DemonSlayer35/Stationnement_intelligent/data_parking/1images/5238d4bbb3d55c86db6f1e46-1600421843-1200x675.jpg

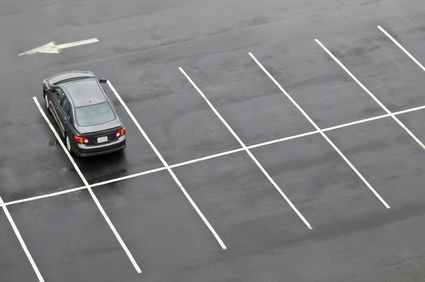
data_parking/1images/5238d4bbb3d55c86db6f1e46-1600421843-1200x675.jpg
