DemonSlayer35/Stationnement_intelligent/data_parking/1images/33248432.webp

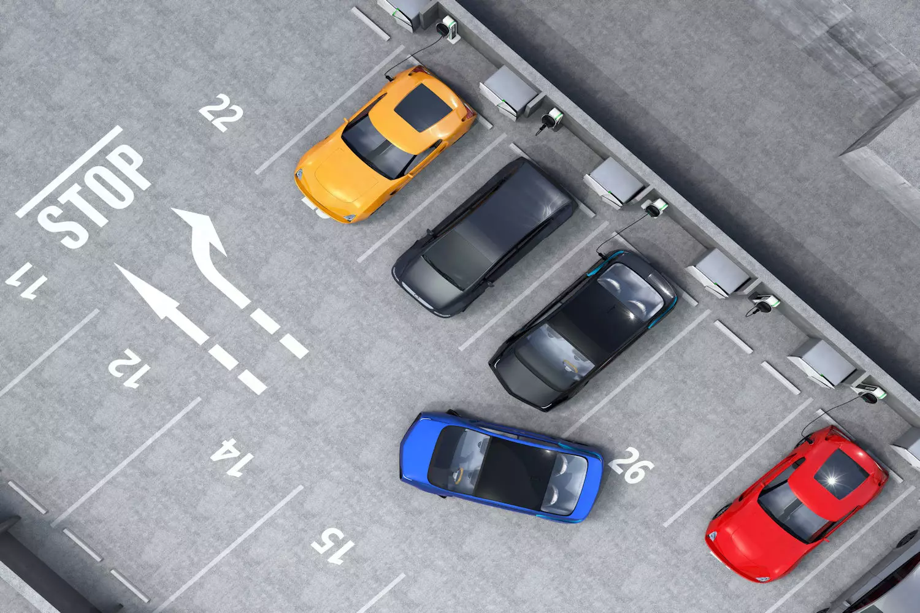
data_parking/1images/33248432.webp
