DemonSlayer35/Stationnement_intelligent/data_parking/1images/_59960313_carparks464_2think.jpg

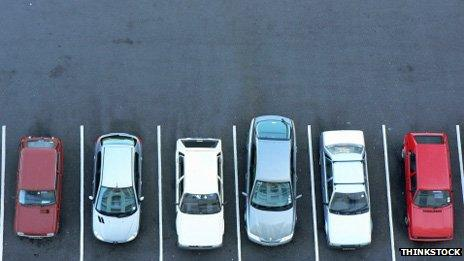
data_parking/1images/_59960313_carparks464_2think.jpg
