DemonSlayer35/Stationnement_intelligent/data_parking/1images/AugustFeaturedImage.jpg

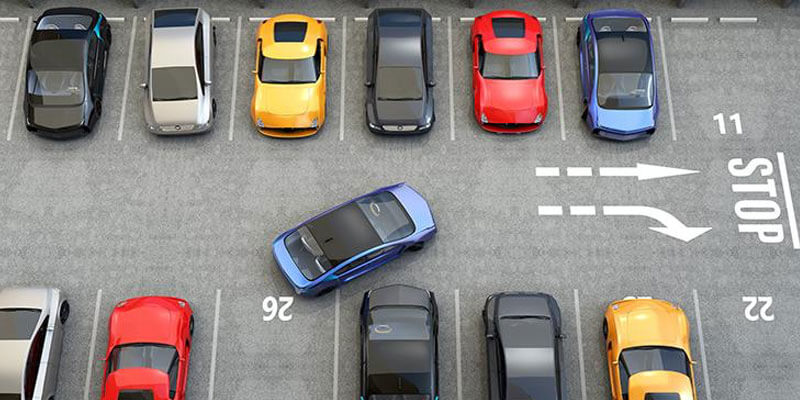
data_parking/1images/AugustFeaturedImage.jpg
