DemonSlayer35/Stationnement_intelligent/data_parking/1images/b-b-hotel-belgium-parking.webp

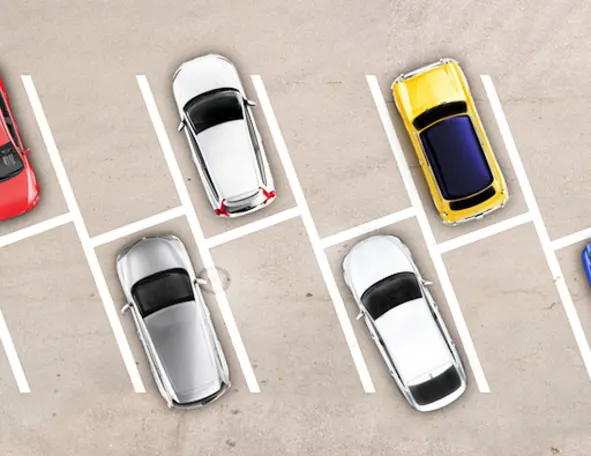
data_parking/1images/b-b-hotel-belgium-parking.webp
