DemonSlayer35/Stationnement_intelligent/data_parking/1images/image.jpg

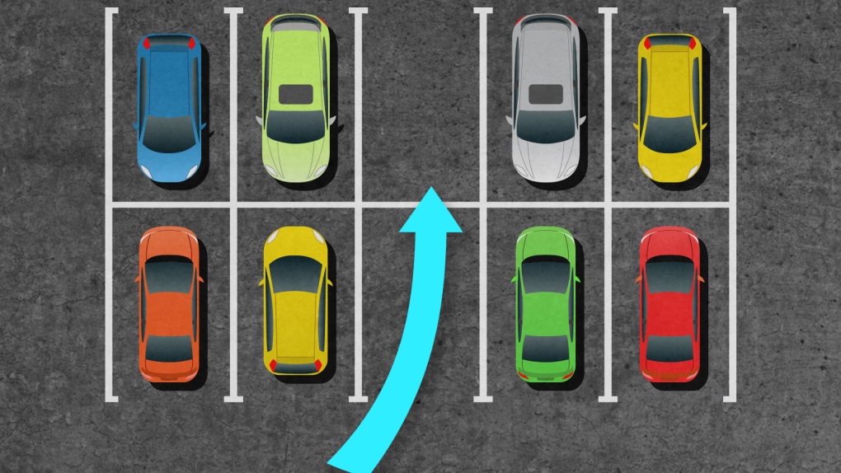
data_parking/1images/image.jpg
