DemonSlayer35/Stationnement_intelligent/data_parking/1images/Norme-Marquage-sol-Parking-en-Bataille.jpg

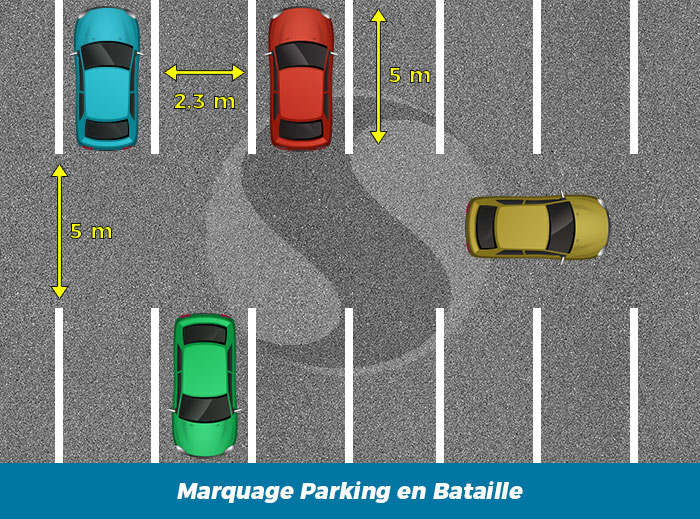
data_parking/1images/Norme-Marquage-sol-Parking-en-Bataille.jpg
