DemonSlayer35/Stationnement_intelligent/data_parking/1images/parking-696x497.jpg

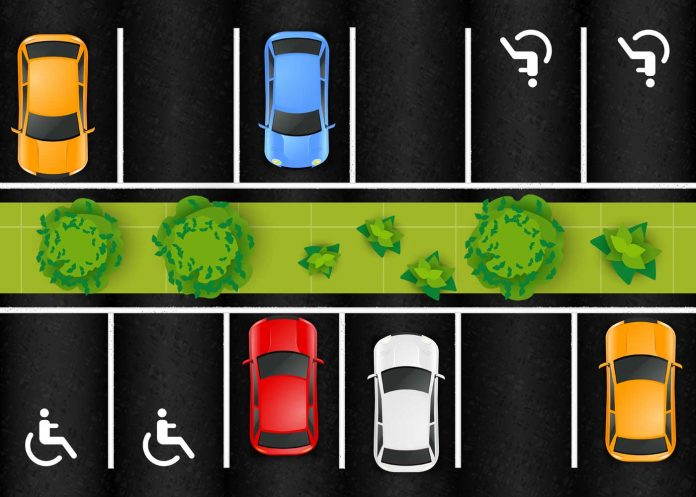
data_parking/1images/parking-696x497.jpg
