DemonSlayer35/Stationnement_intelligent/data_parking/1images/parking-lot-4928423.jpg

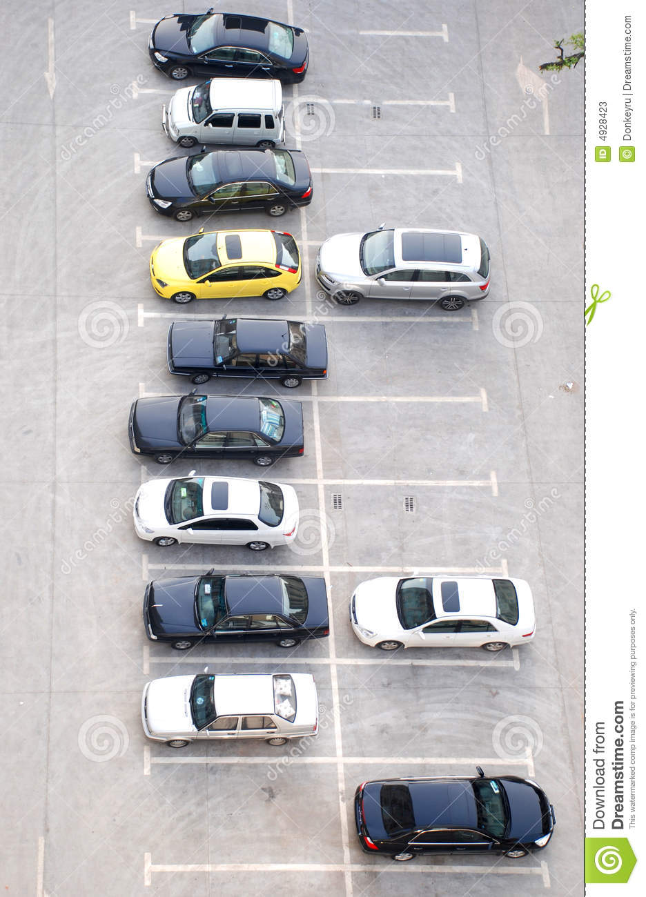
data_parking/1images/parking-lot-4928423.jpg
