DemonSlayer35/Stationnement_intelligent/data_parking/1images/parkinglot_outdoor_GettyImages-915375802.jpg

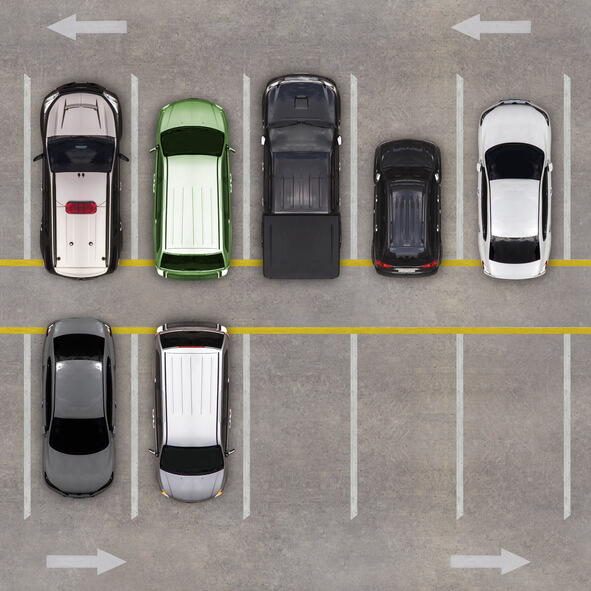
data_parking/1images/parkinglot_outdoor_GettyImages-915375802.jpg
