DemonSlayer35/Stationnement_intelligent/data_parking/1images/parkings-publics.jpg

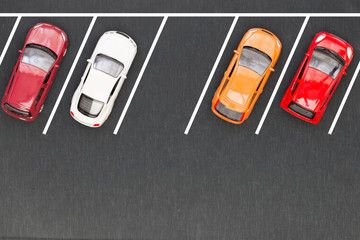
data_parking/1images/parkings-publics.jpg
