DemonSlayer35/Stationnement_intelligent/data_parking/images/WIN_20230214_13_56_52_Pro.jpg

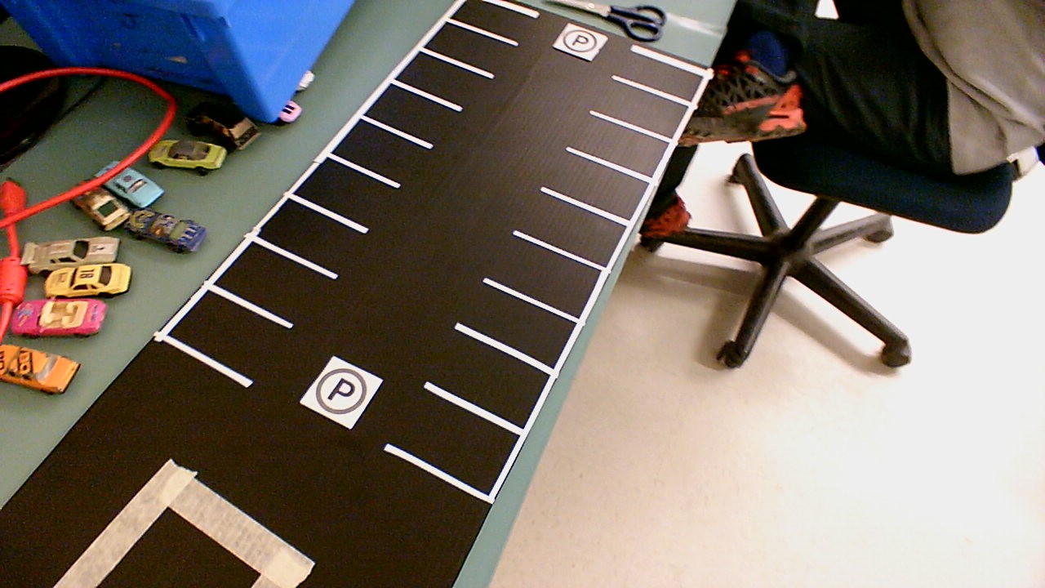
data_parking/images/WIN_20230214_13_56_52_Pro.jpg
