DemonSlayer35/Stationnement_intelligent/data_parking/images/WIN_20230214_13_57_07_Pro.jpg

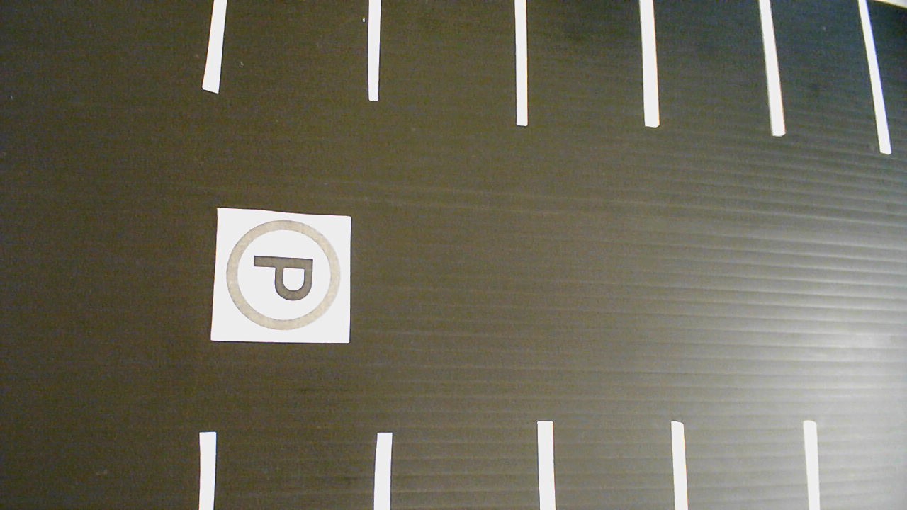
data_parking/images/WIN_20230214_13_57_07_Pro.jpg
