DemonSlayer35/Stationnement_intelligent/data_parking/images_backup/IMG_1646.jpg

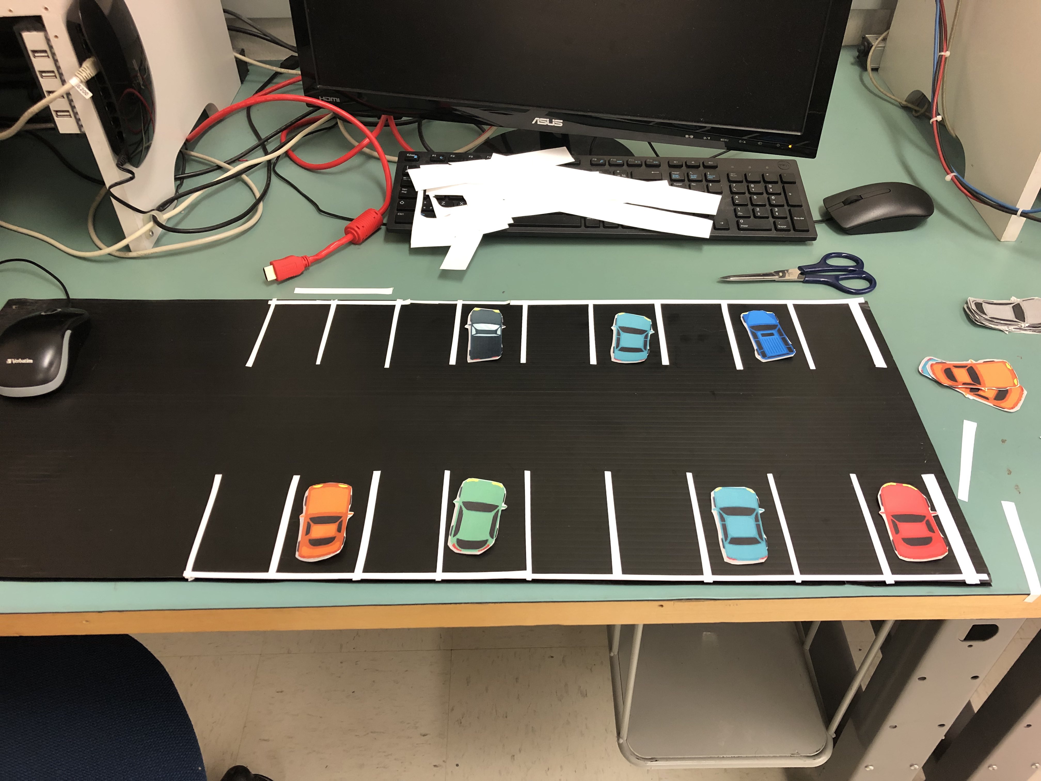
data_parking/images_backup/IMG_1646.jpg
