DemonSlayer35/Stationnement_intelligent/data_parking/images_backup/IMG_1647.jpg

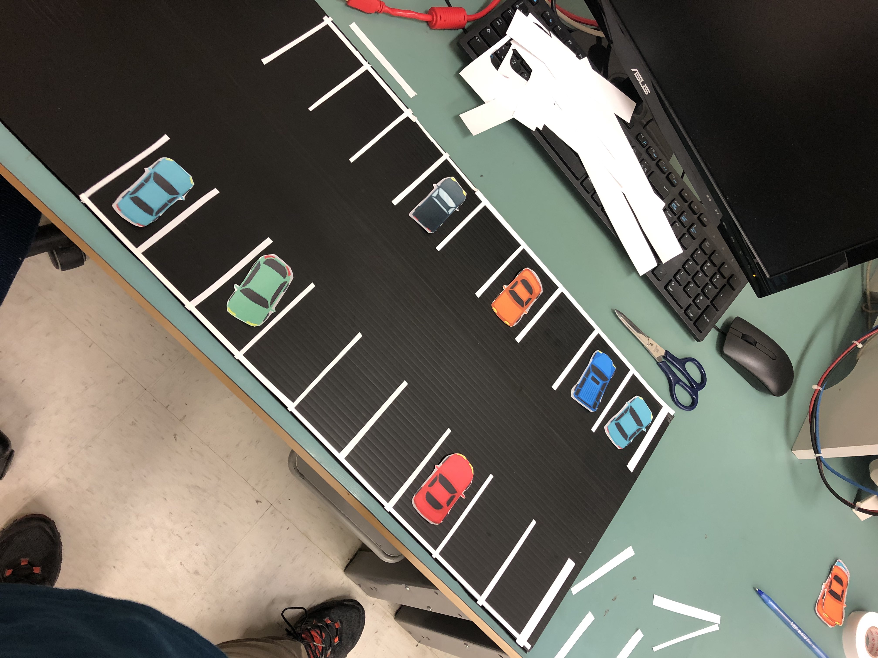
data_parking/images_backup/IMG_1647.jpg
