DemonSlayer35/Stationnement_intelligent/data_parking/images_backup/IMG_1648.jpg

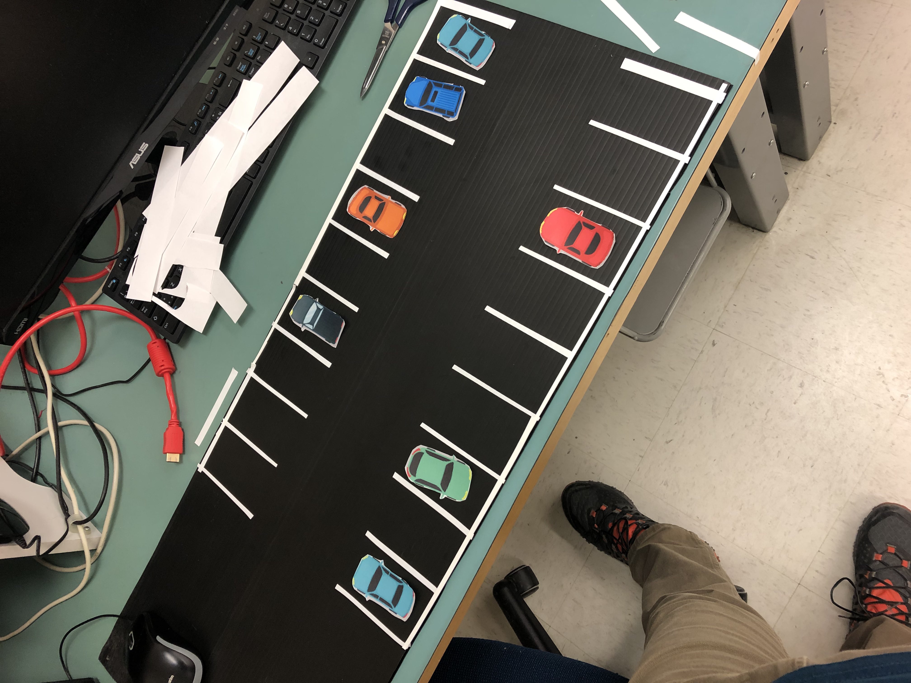
data_parking/images_backup/IMG_1648.jpg
