DemonSlayer35/Stationnement_intelligent/data_parking/imagesParking/WIN_20230207_09_41_29_Pro.jpg

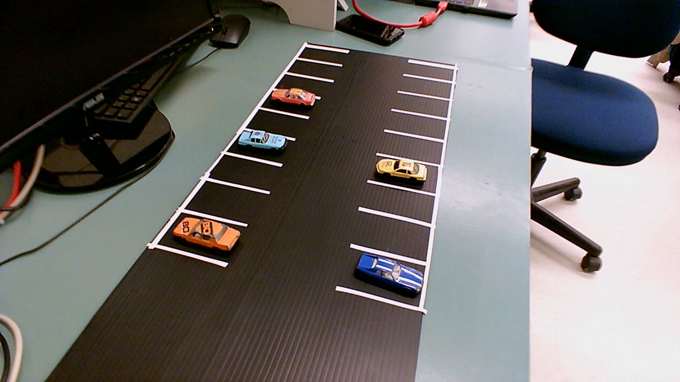
data_parking/imagesParking/WIN_20230207_09_41_29_Pro.jpg
