DemonSlayer35/Stationnement_intelligent/data_parking/imagesParking/WIN_20230207_12_37_04_Pro.jpg

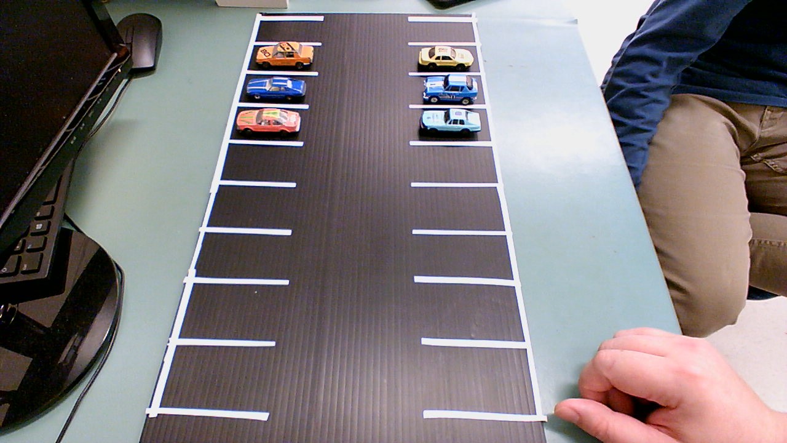
data_parking/imagesParking/WIN_20230207_12_37_04_Pro.jpg
