DemonSlayer35/Stationnement_intelligent/data_parking/imagesParking/WIN_20230207_13_53_06_Pro.jpg

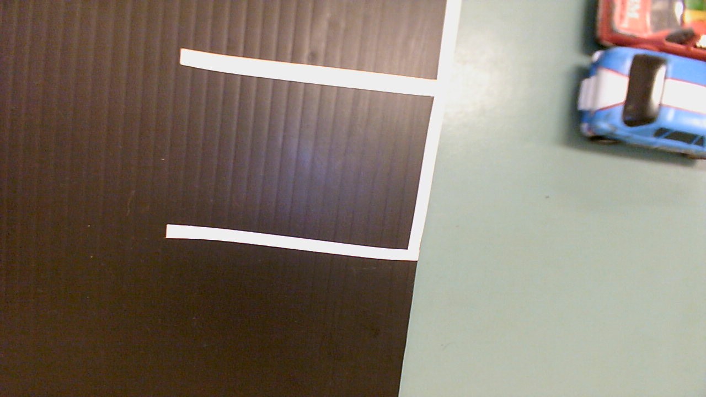
data_parking/imagesParking/WIN_20230207_13_53_06_Pro.jpg
